ItsKarlito/healthyleaves/software/screenshots/editPlantFromCatalog.png

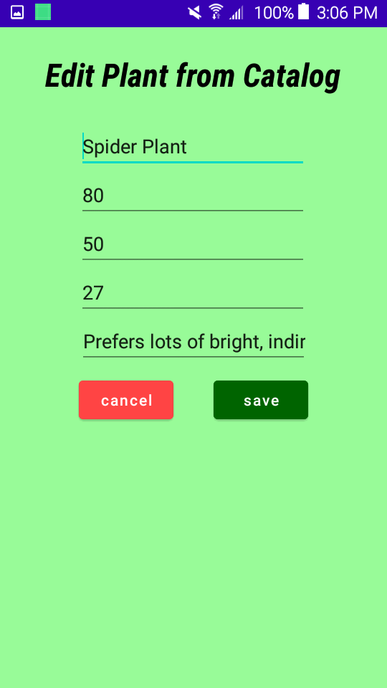
software/screenshots/editPlantFromCatalog.png
