ItsKarlito/healthyleaves/software/screenshots/plantCatalog2.png

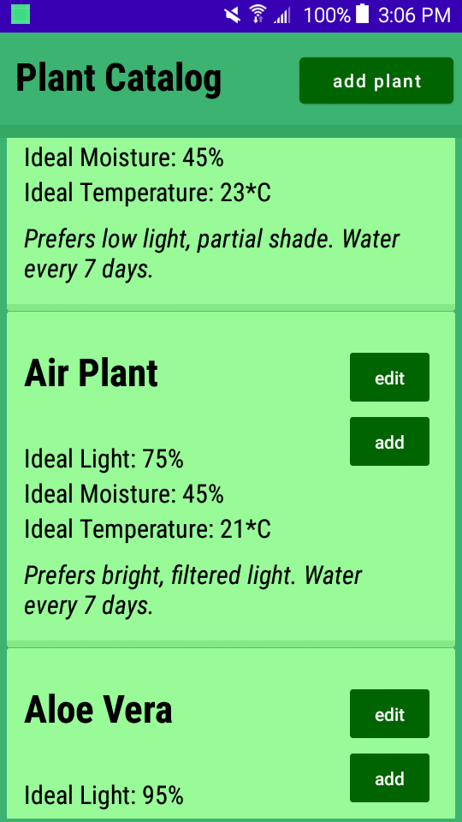
software/screenshots/plantCatalog2.png
