ItsKarlito/healthyleaves/software/screenshots/sunflower.png

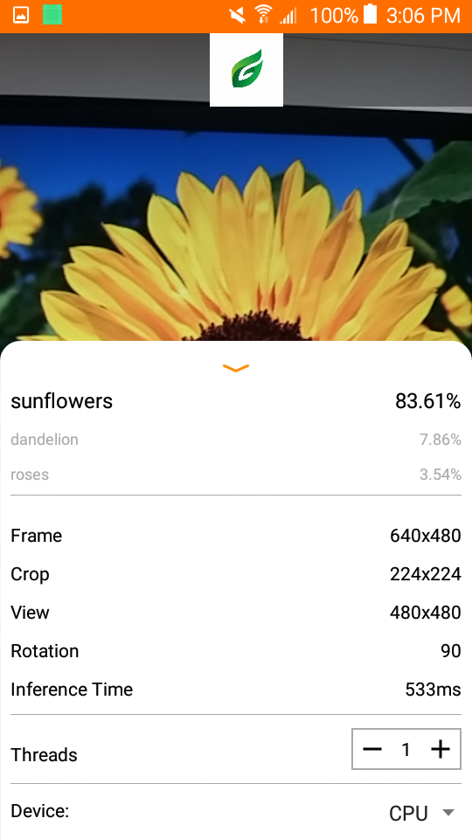
software/screenshots/sunflower.png
