ItsKarlito/healthyleaves/hardware/sparkfunESP32/HealthyLeaves/getEpochTime.ino

//function returns real time from previous timestamp

int getEpochTime()
{
  struct tm timeInfo;
  if (!getLocalTime(&timeInfo))
  {
    return -1;
  }
  time_t timeSinceEpoch = mktime(&timeInfo);
  return timeSinceEpoch;
}
